amaaliiiiiiiia/Proiect-InkTime-TSC/Images/dispozitiv_final2.jpeg

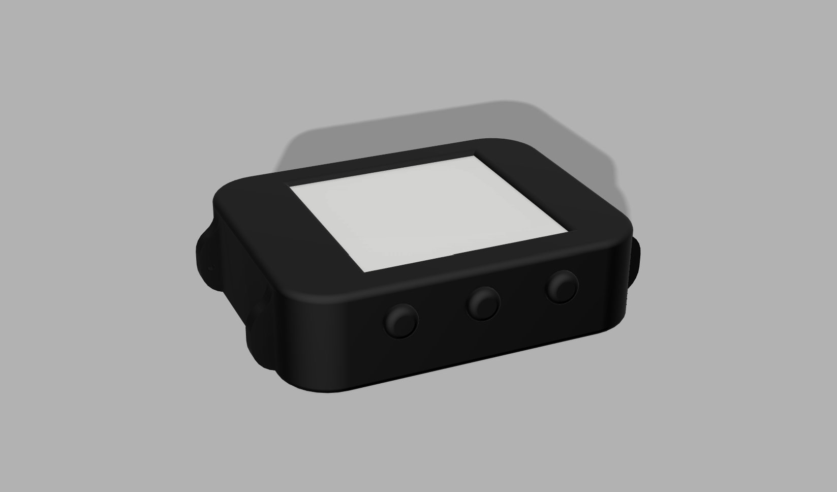
Images/dispozitiv_final2.jpeg
