amaaliiiiiiiia/Proiect-InkTime-TSC/Images/exploded_view1.jpeg

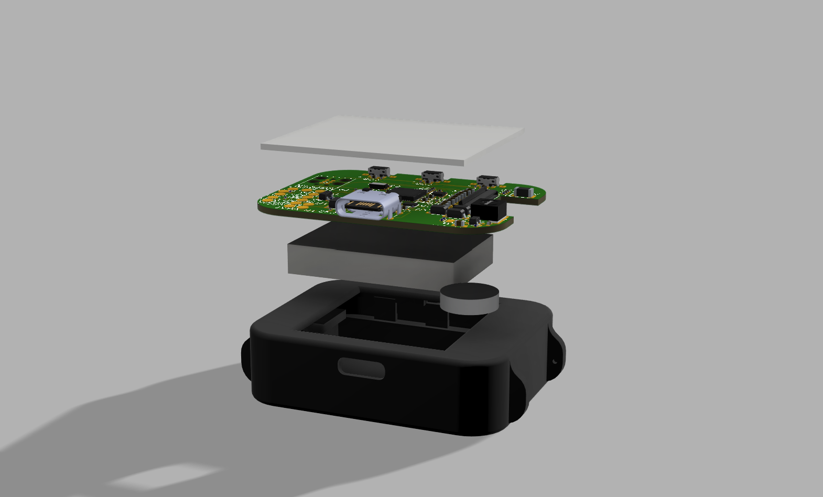
Images/exploded_view1.jpeg
